danwerner21/CortexPC/images/image1.jpg

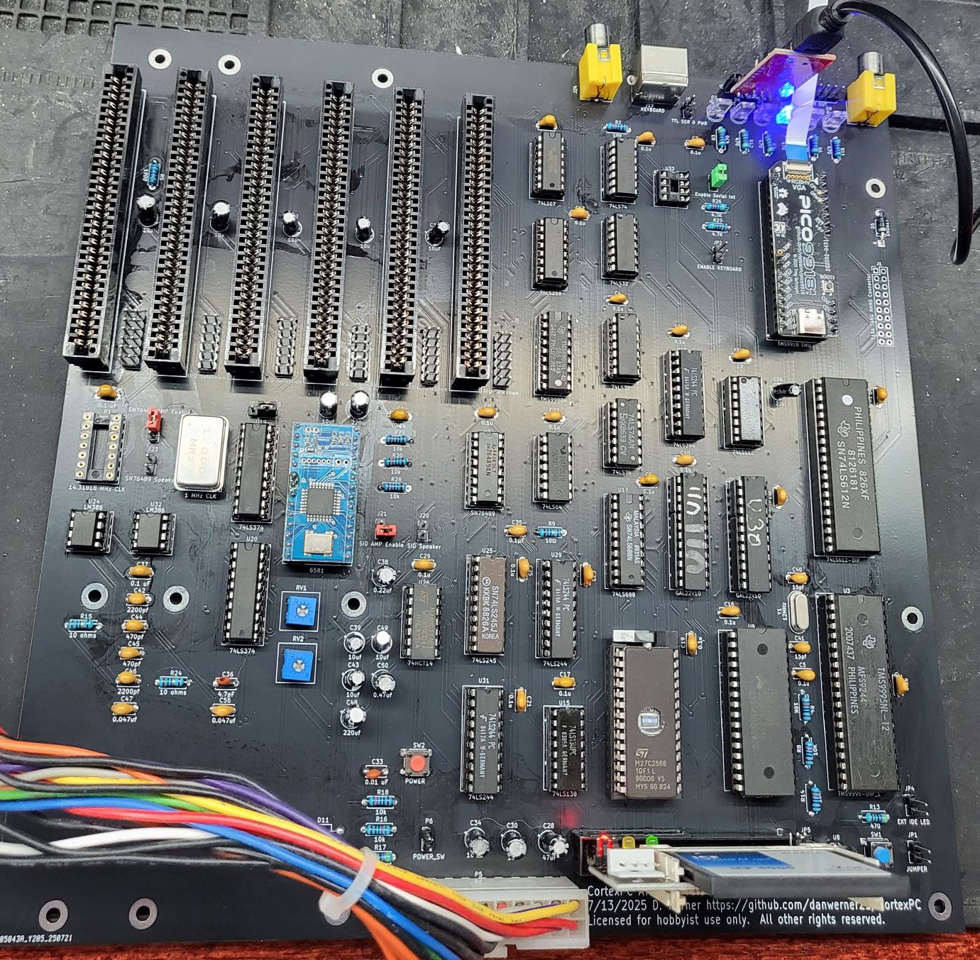
images/image1.jpg
