danwerner21/CortexPC/images/image2.jpg

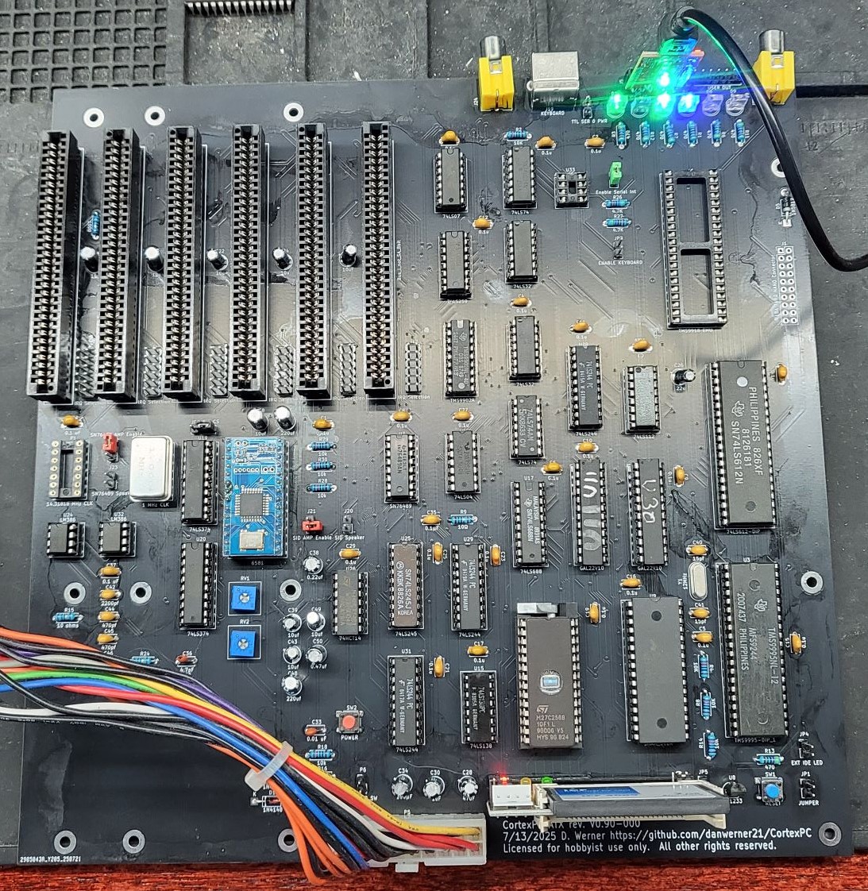
images/image2.jpg
