danwerner21/CortexPC/Hardware/PCB_V0.5.pdf

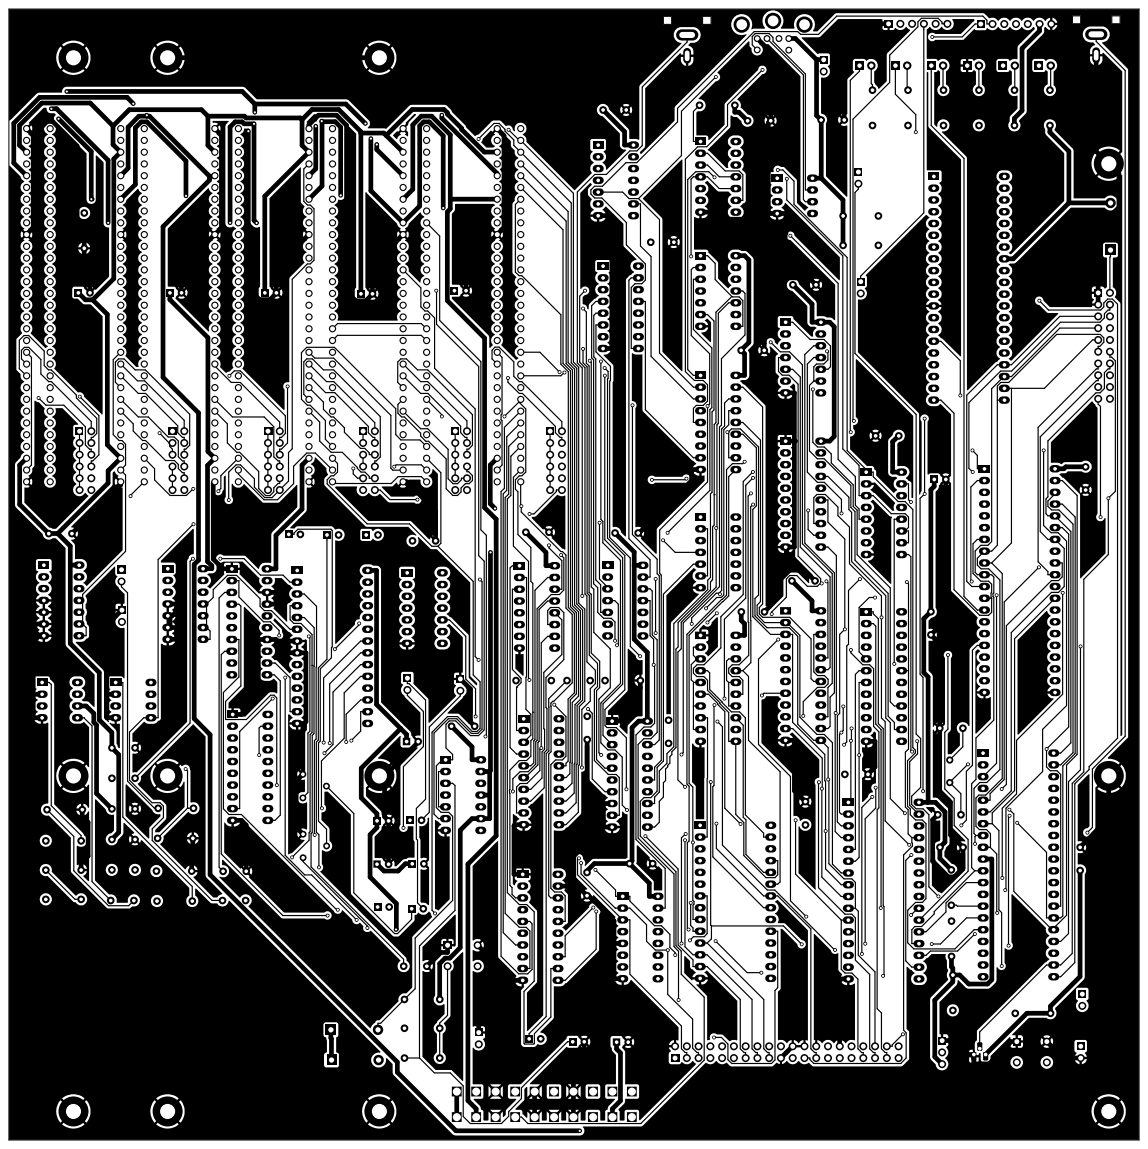
[picture p17: page 1]

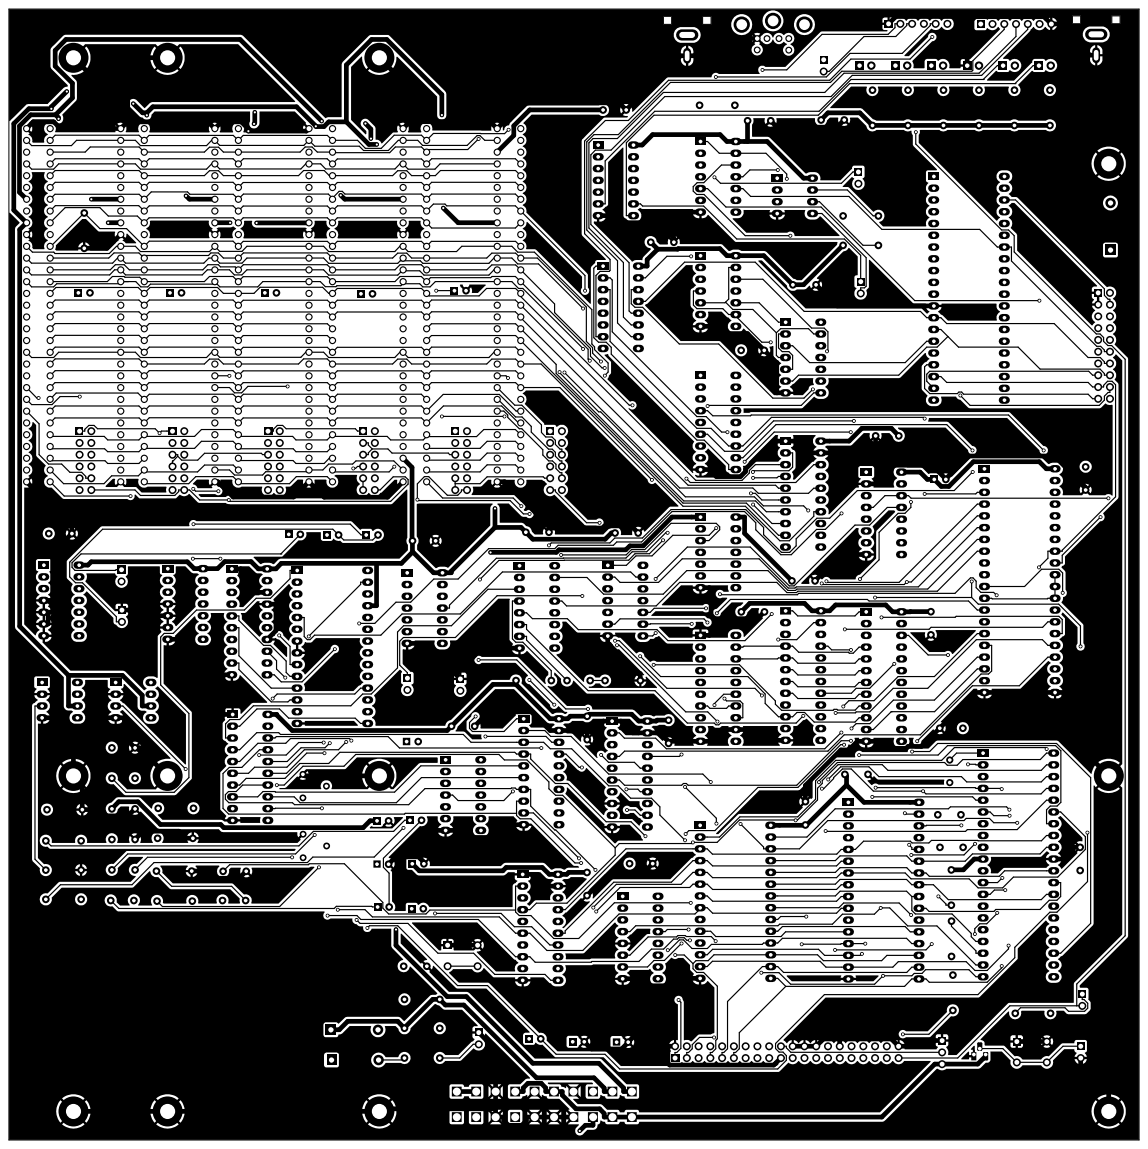
[picture p18: page 2]

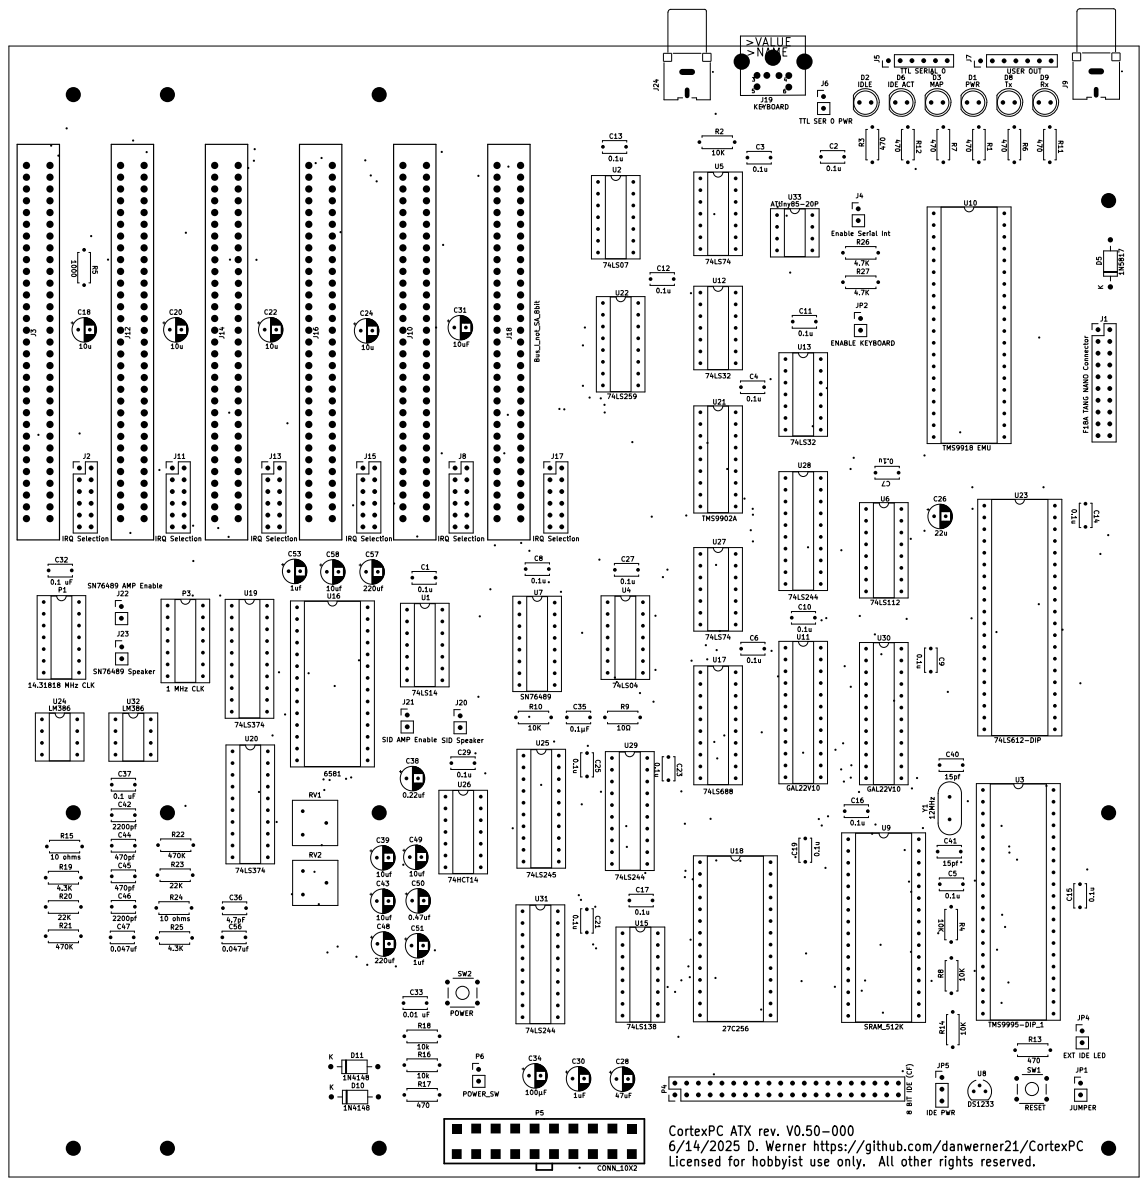
[picture p19: page 3]

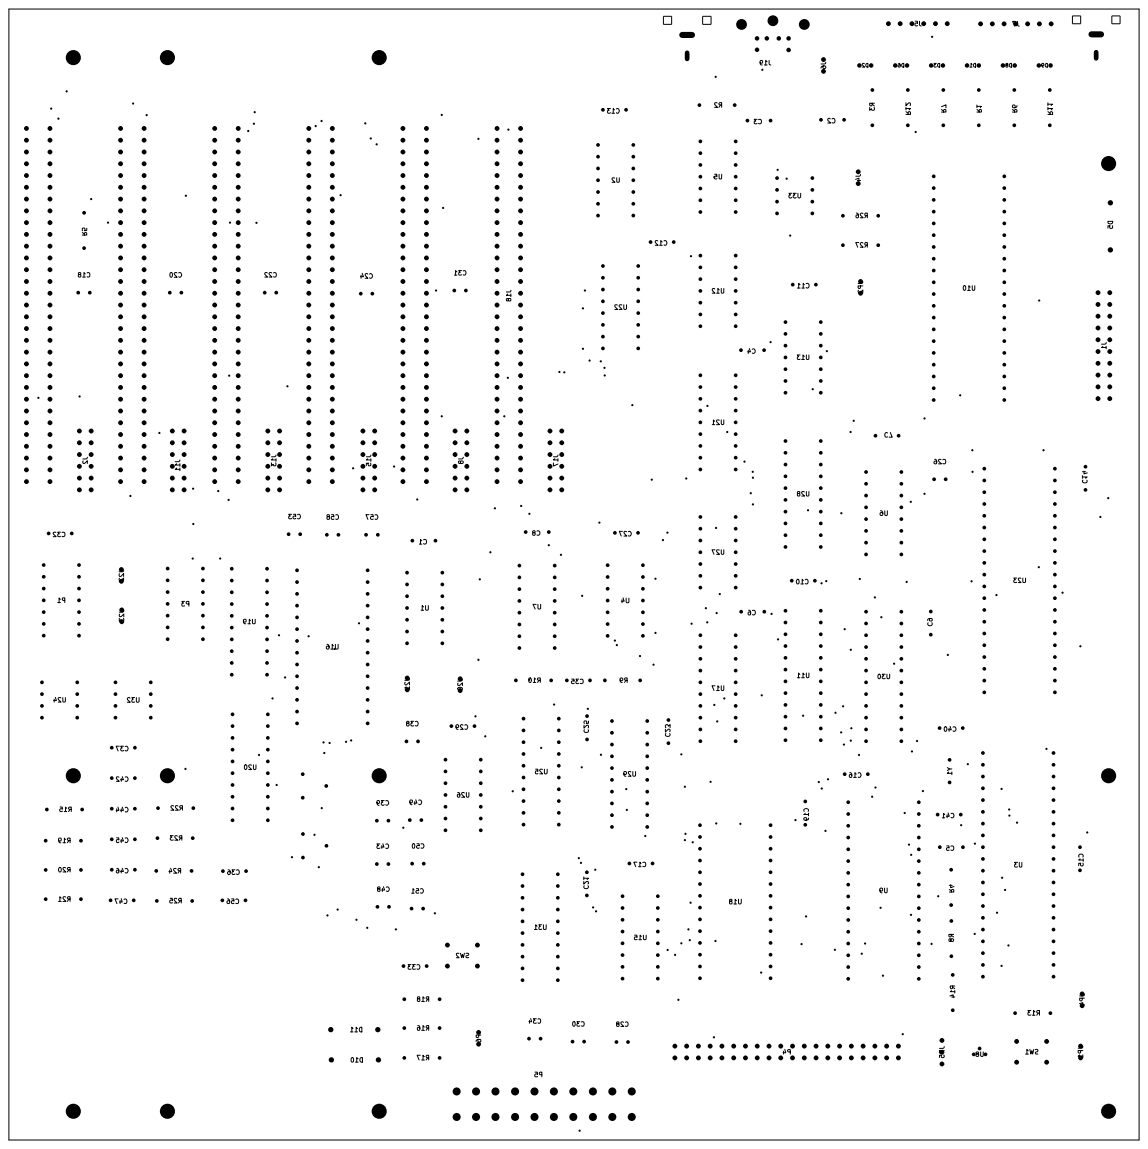
[picture p20: page 4]

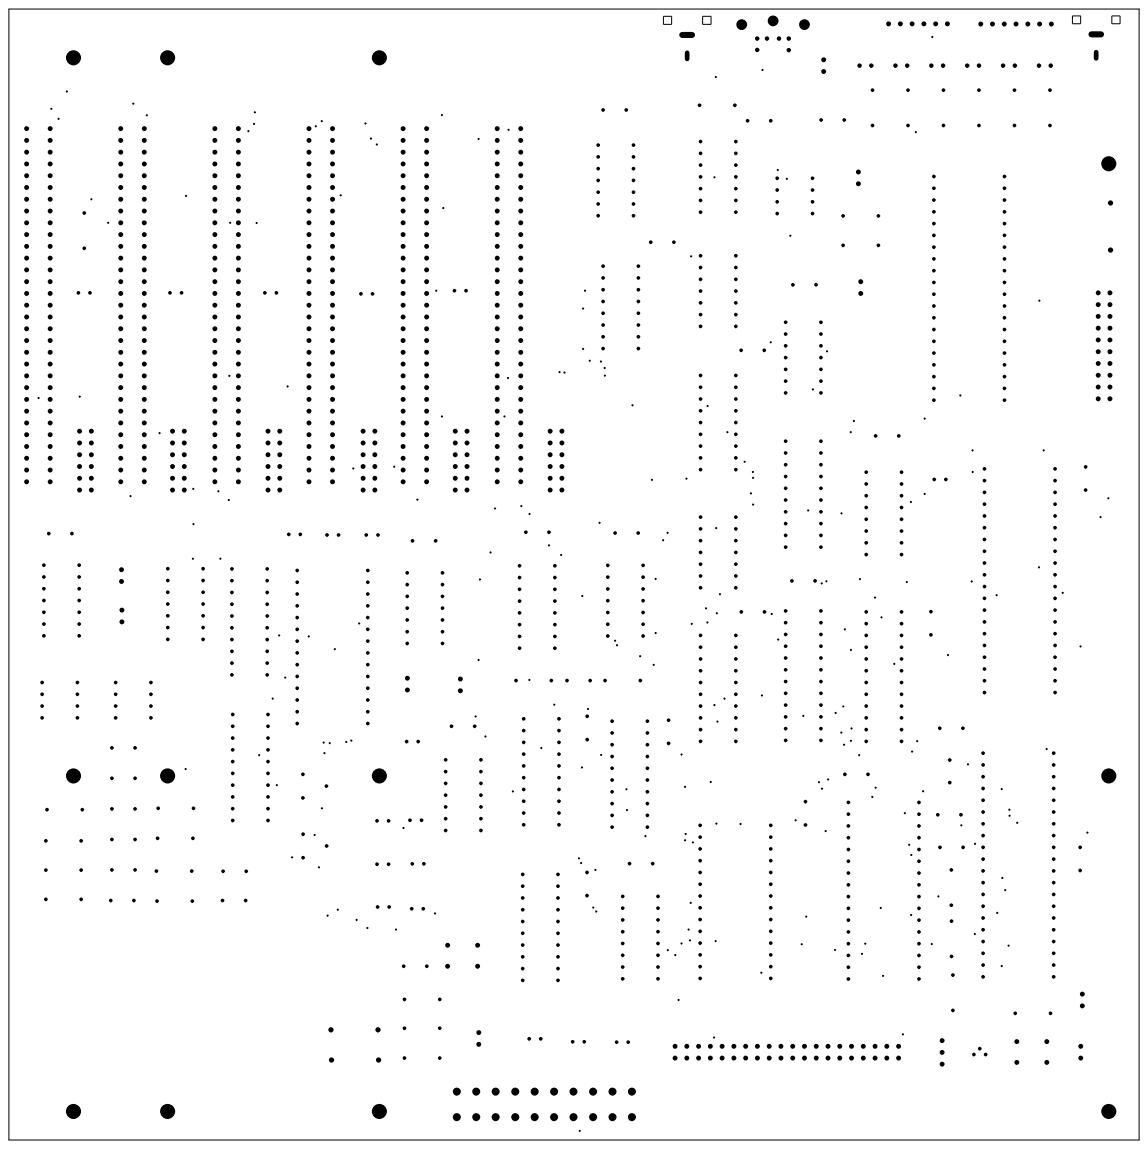
[picture p21: page 5]

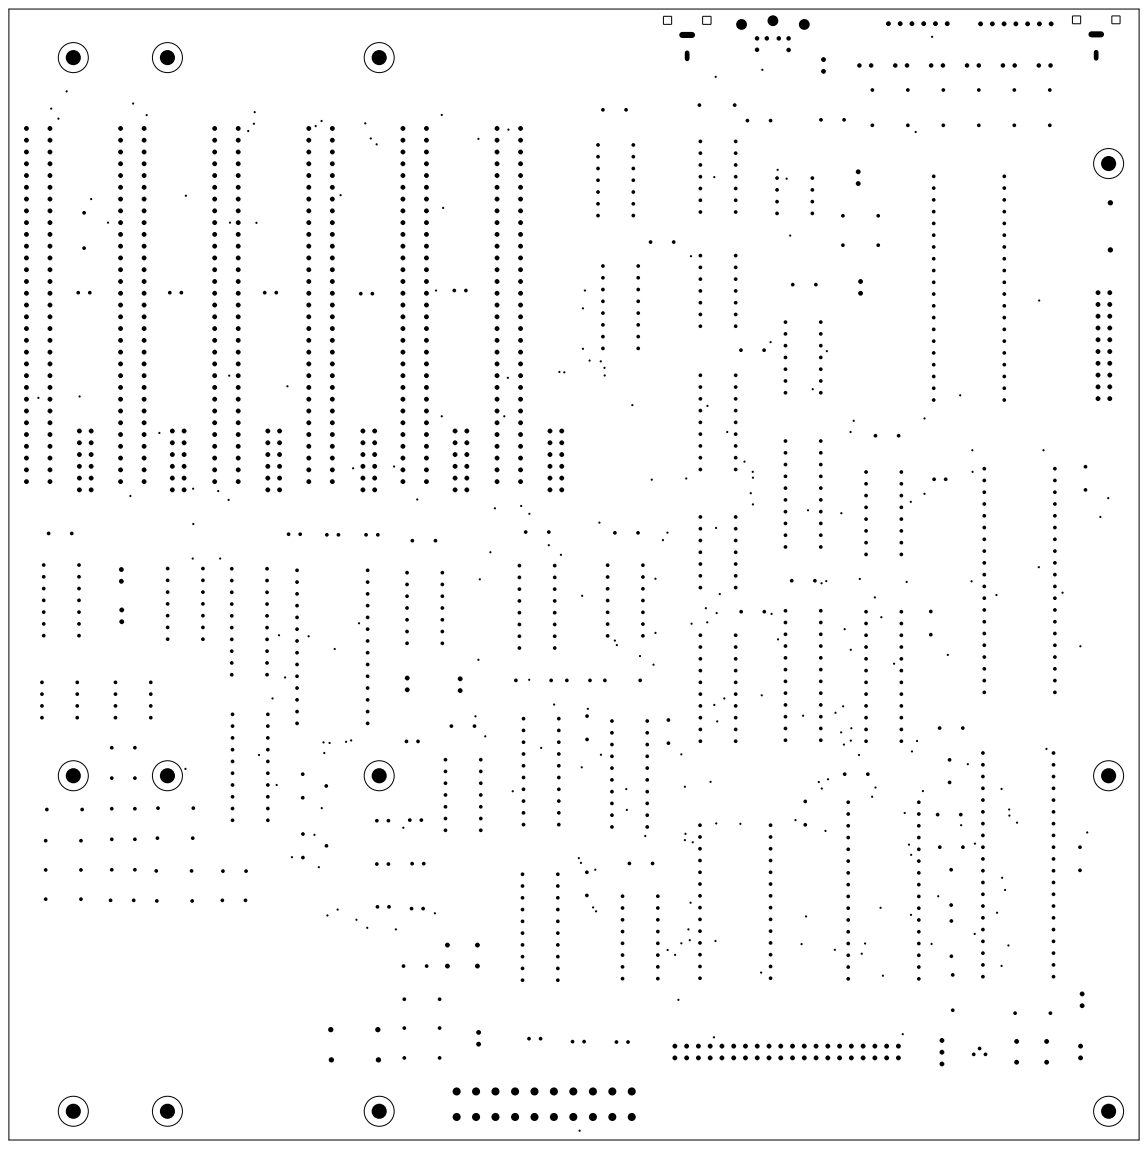
[picture p22: page 6]
