danwerner21/CortexPC/Hardware/Schematic_V0.5.pdf

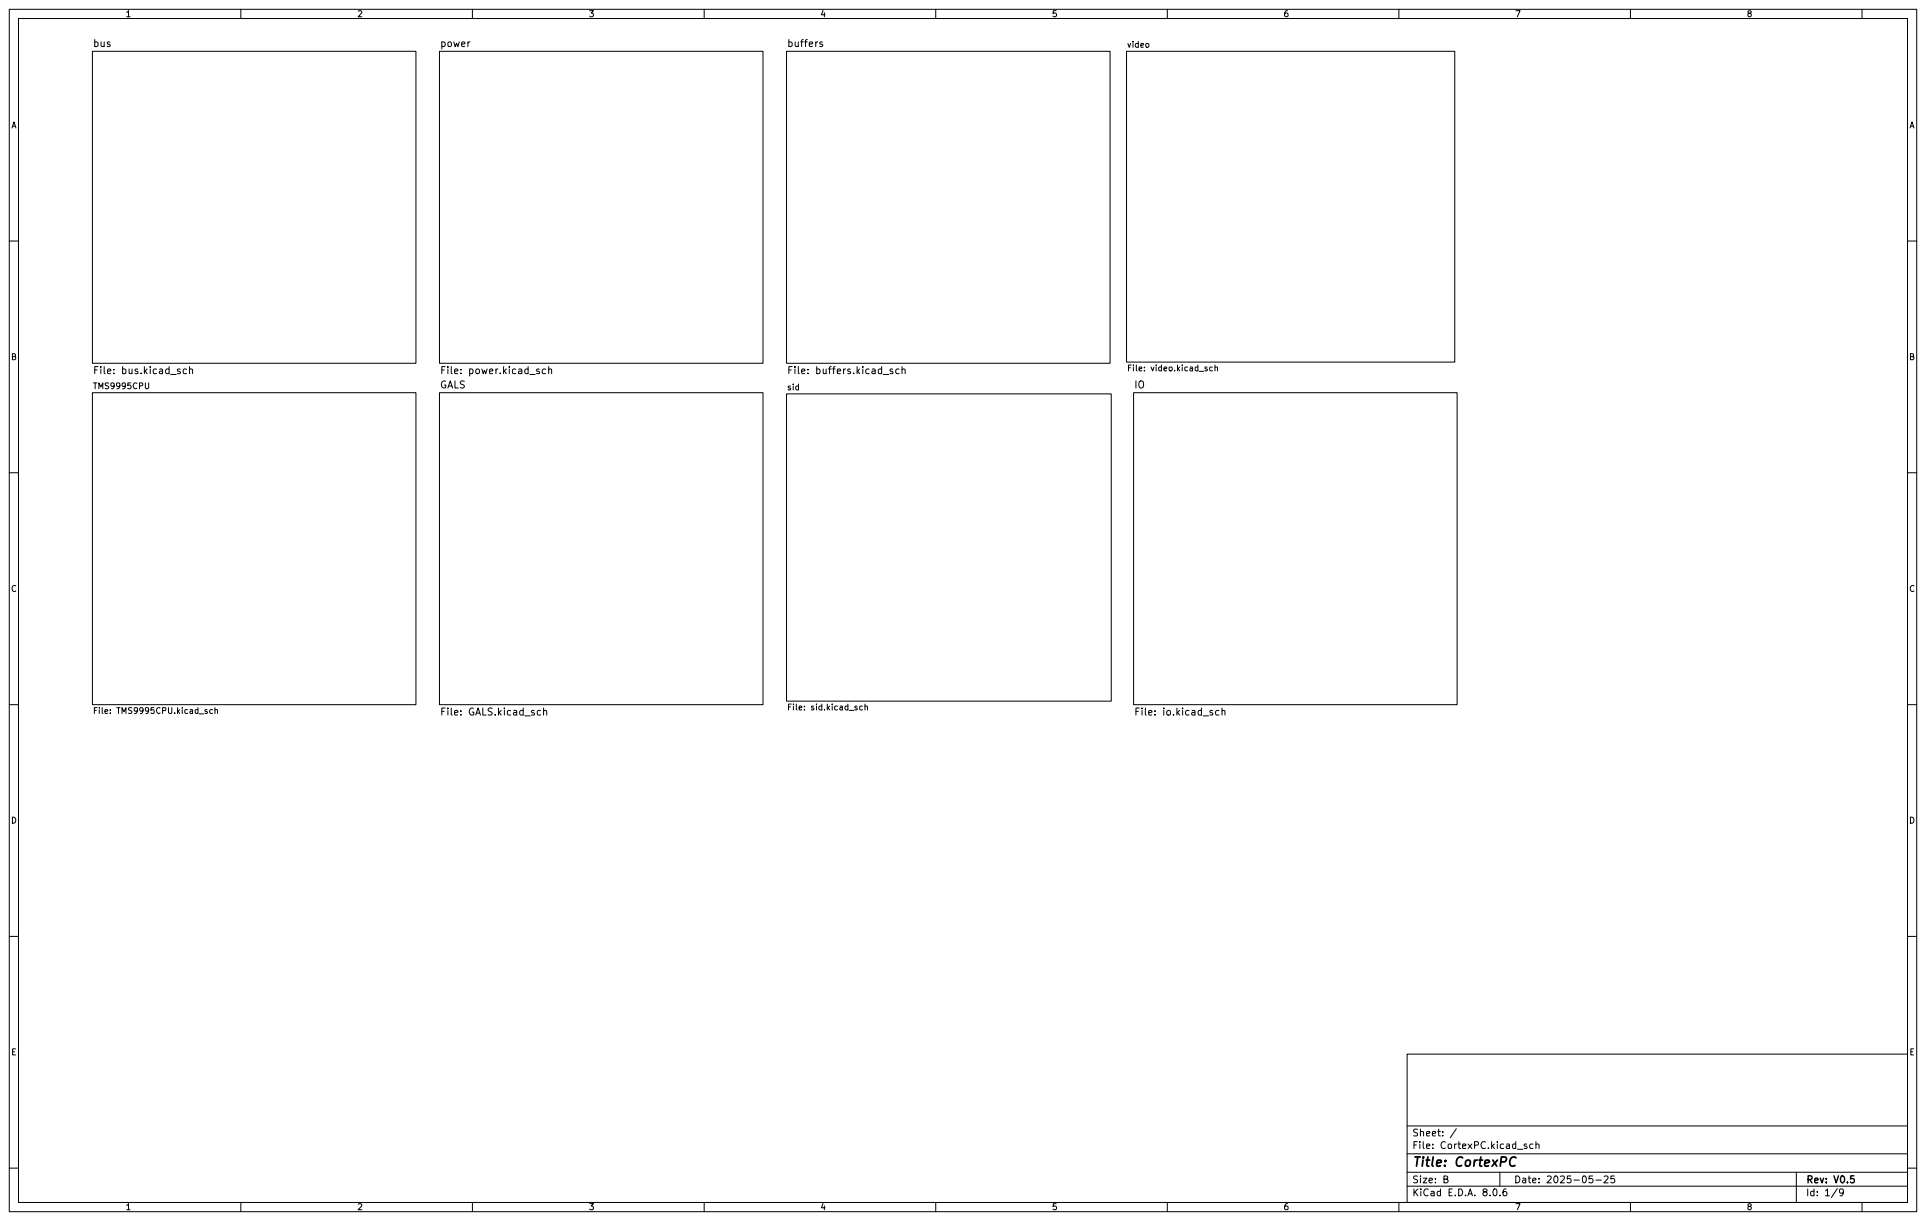
[picture p23: page 1]

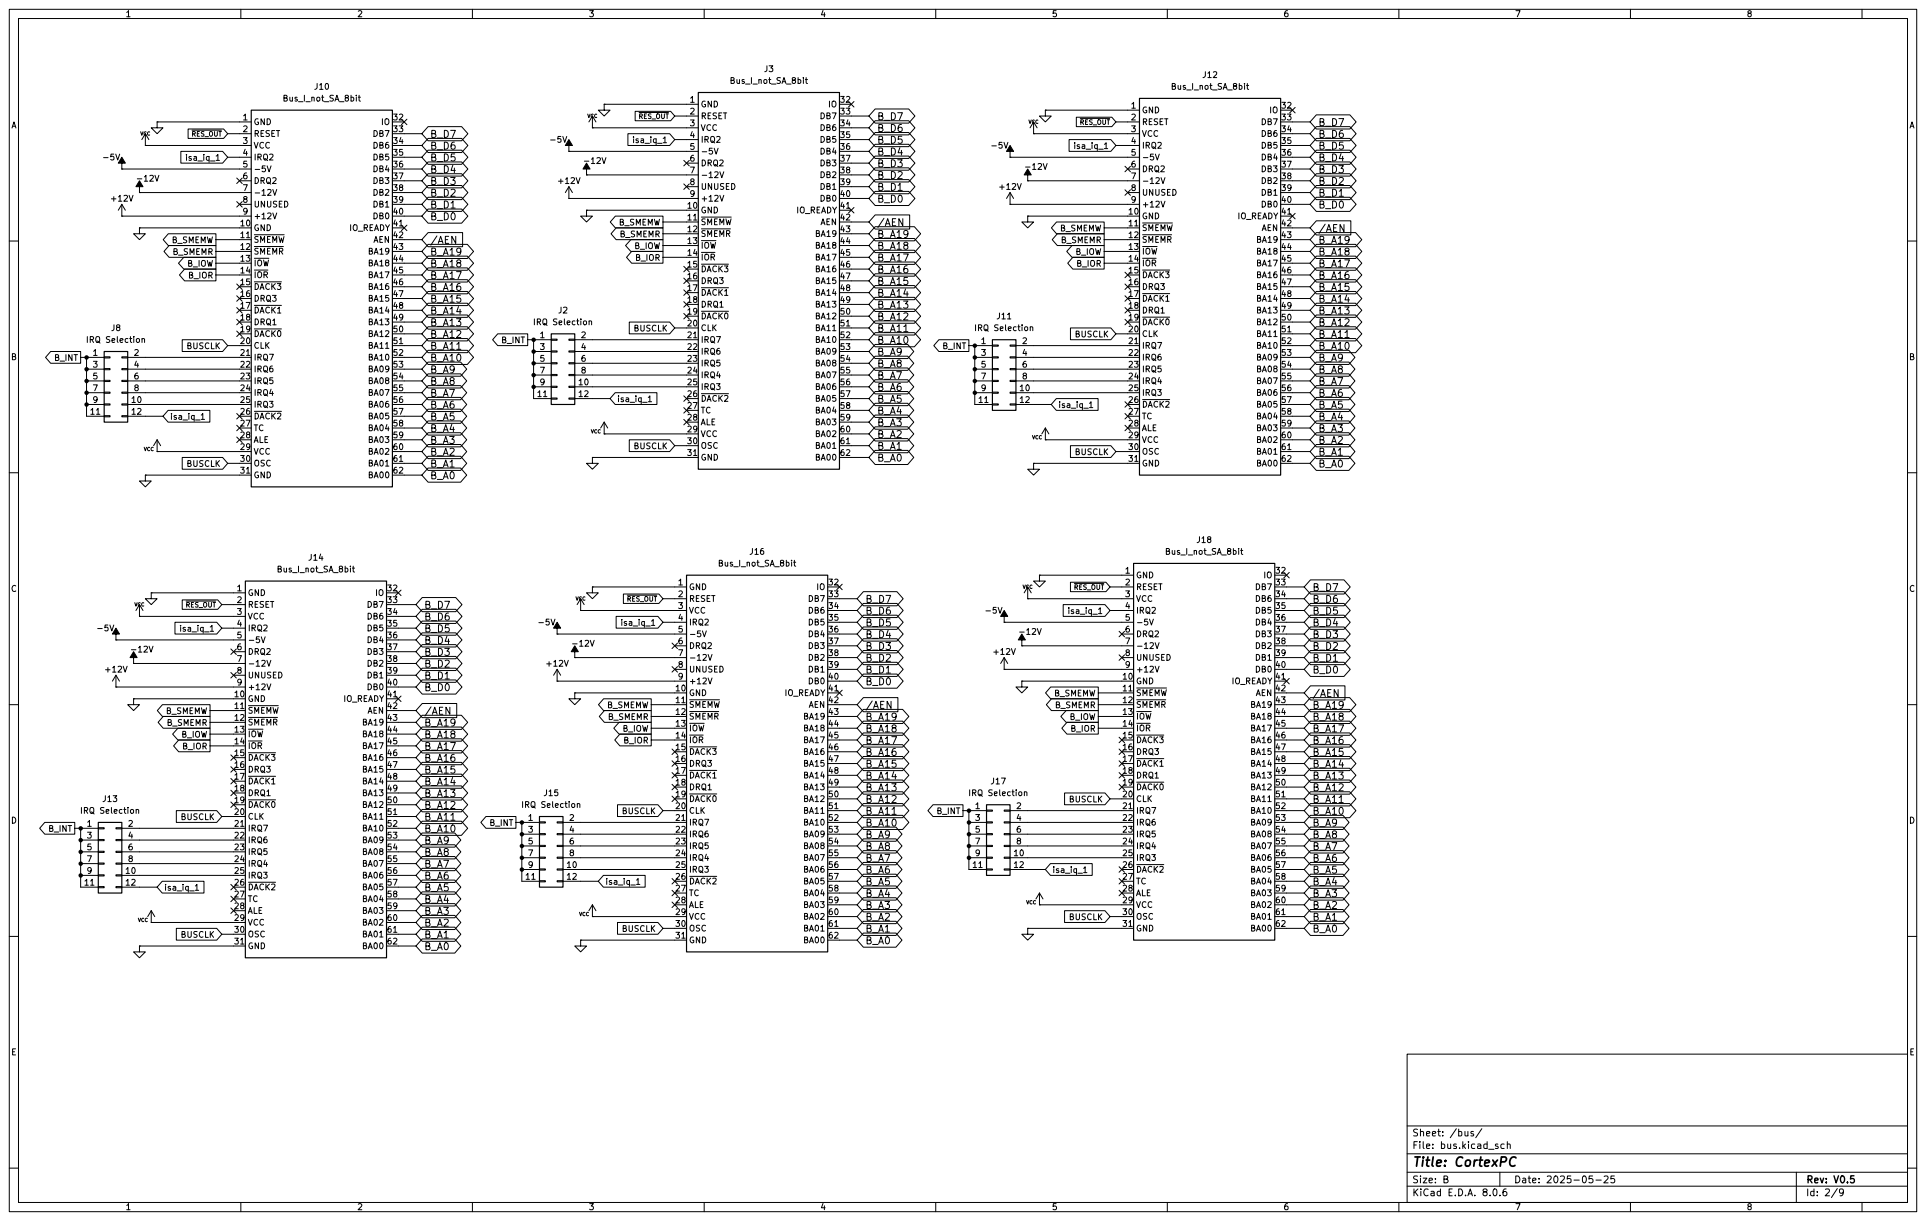
[picture p24: page 2]

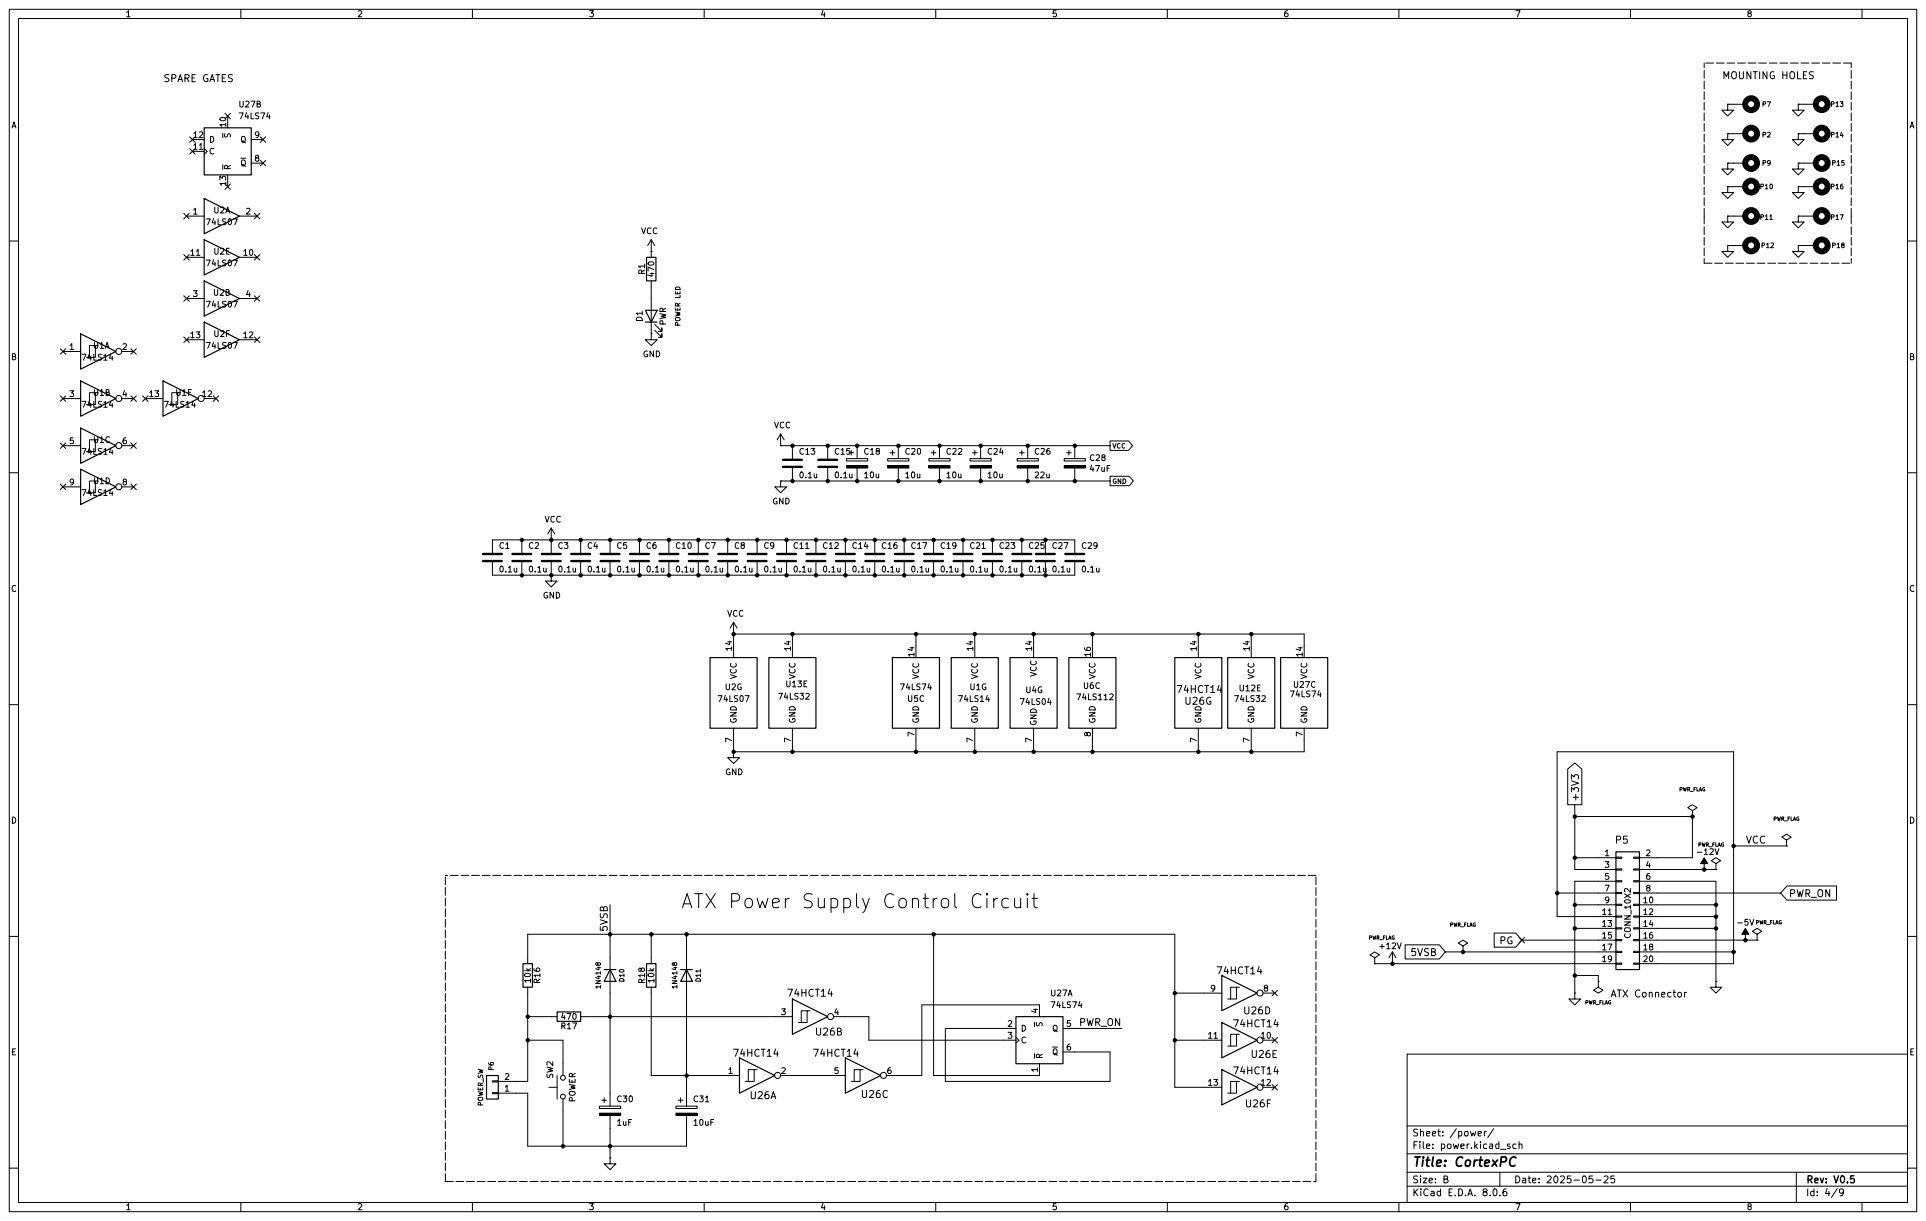
[picture p25: page 3]

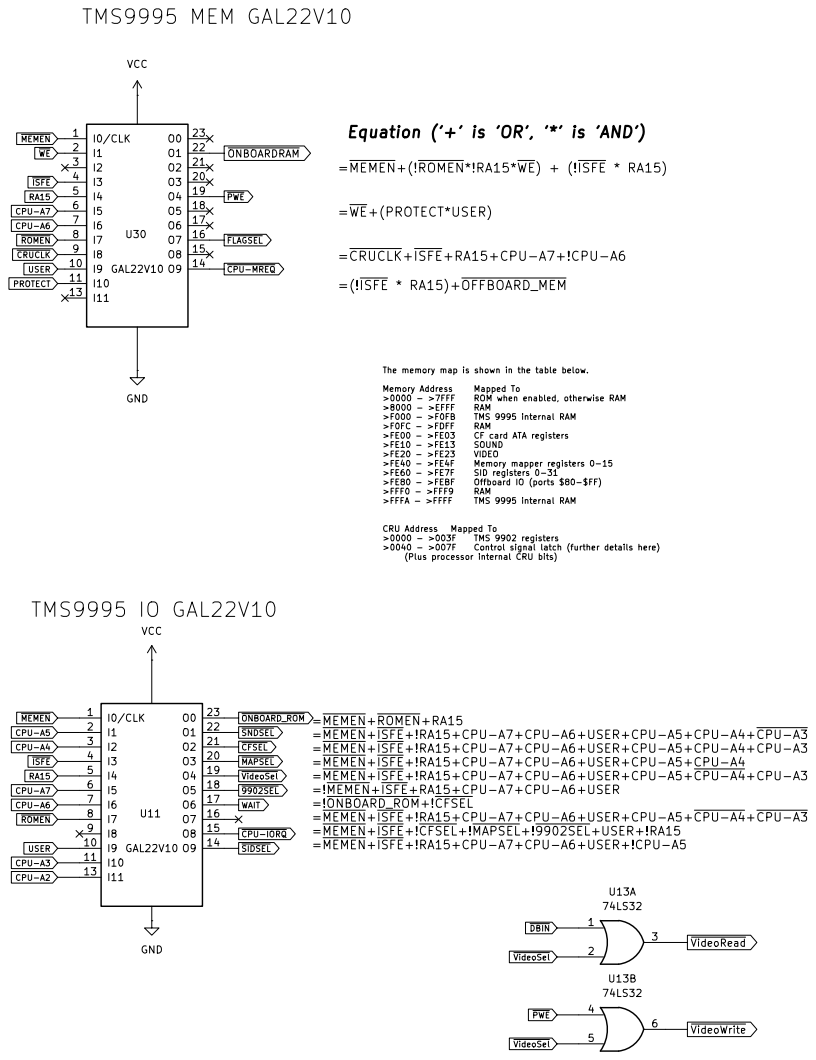
[picture p26: page 4]

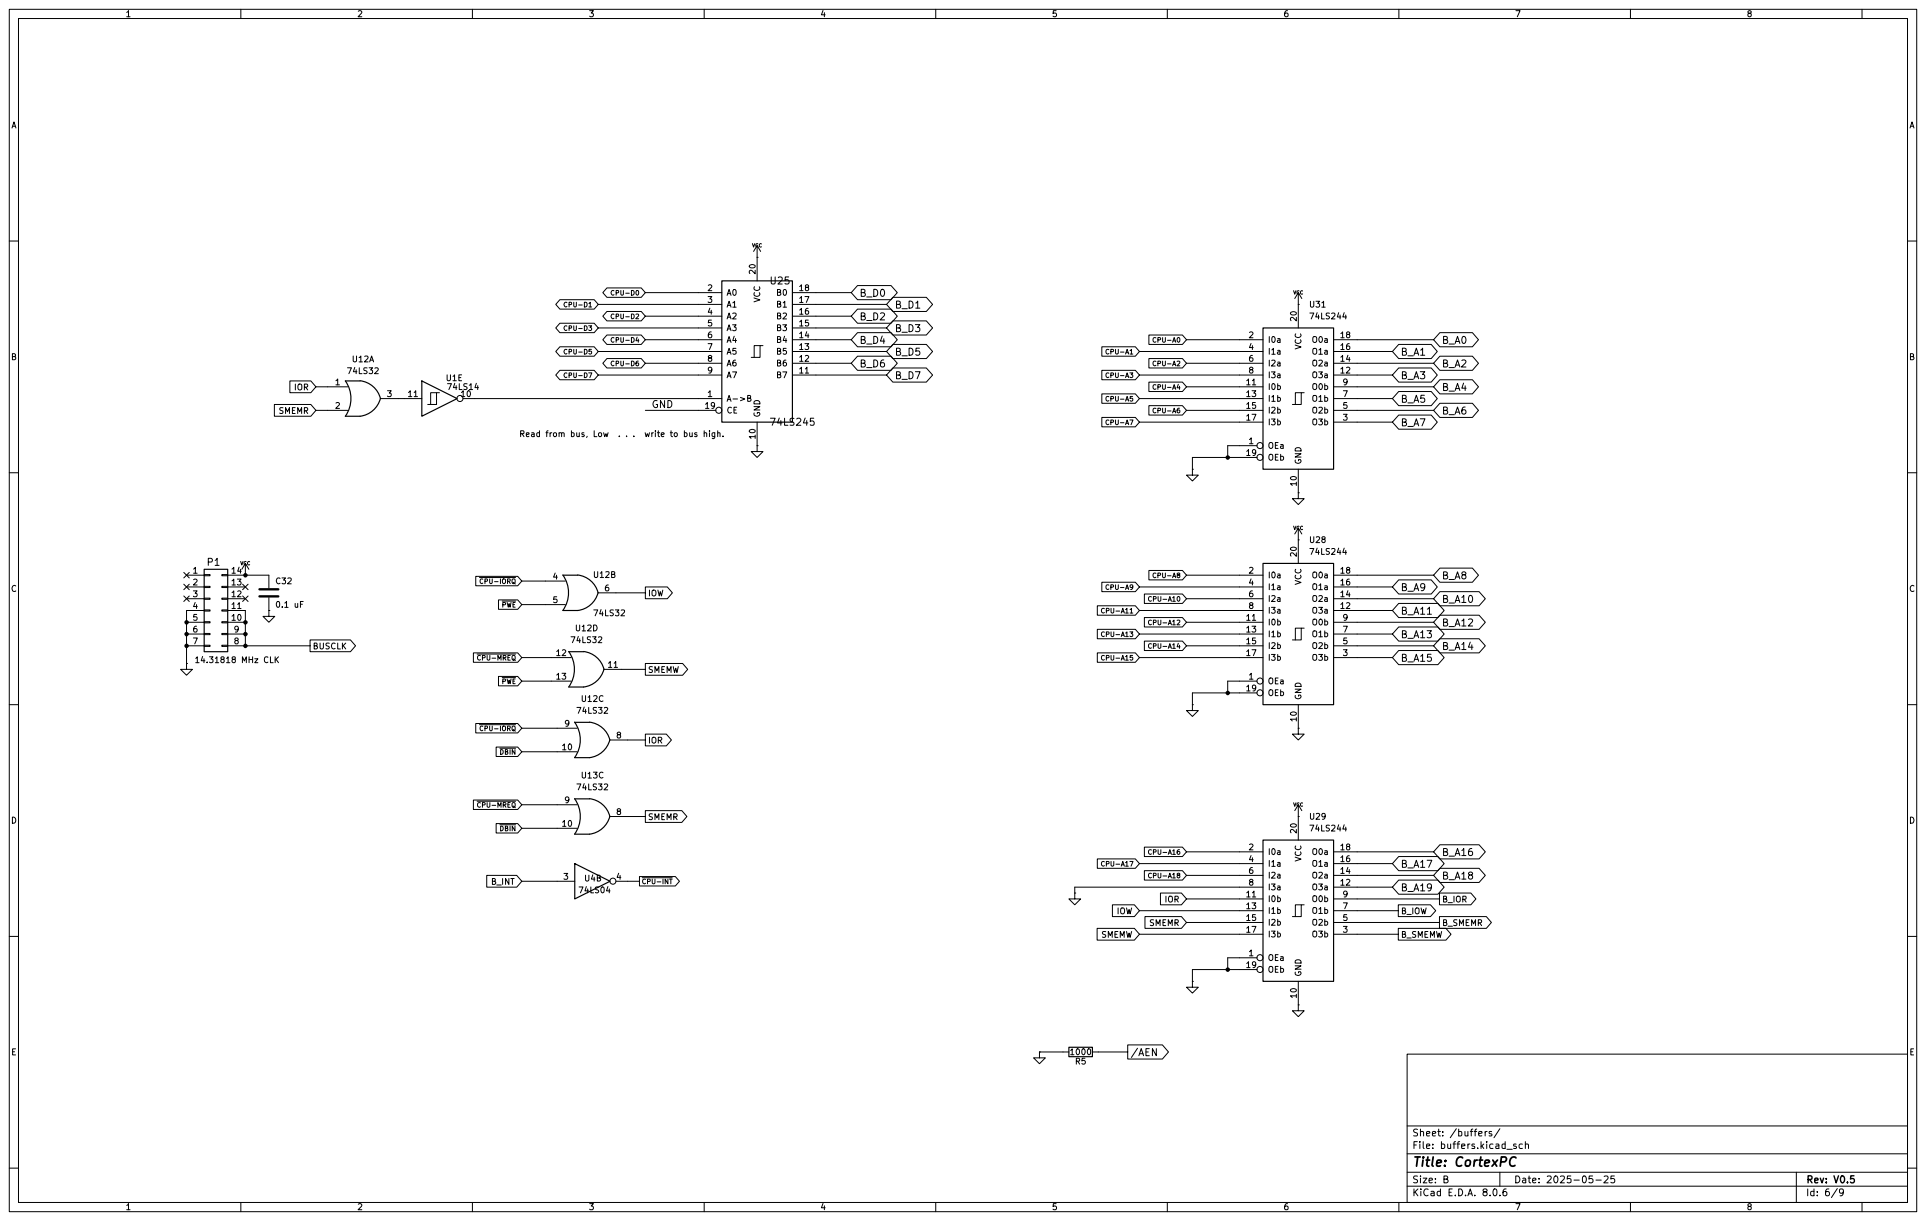
[picture p27: page 5]

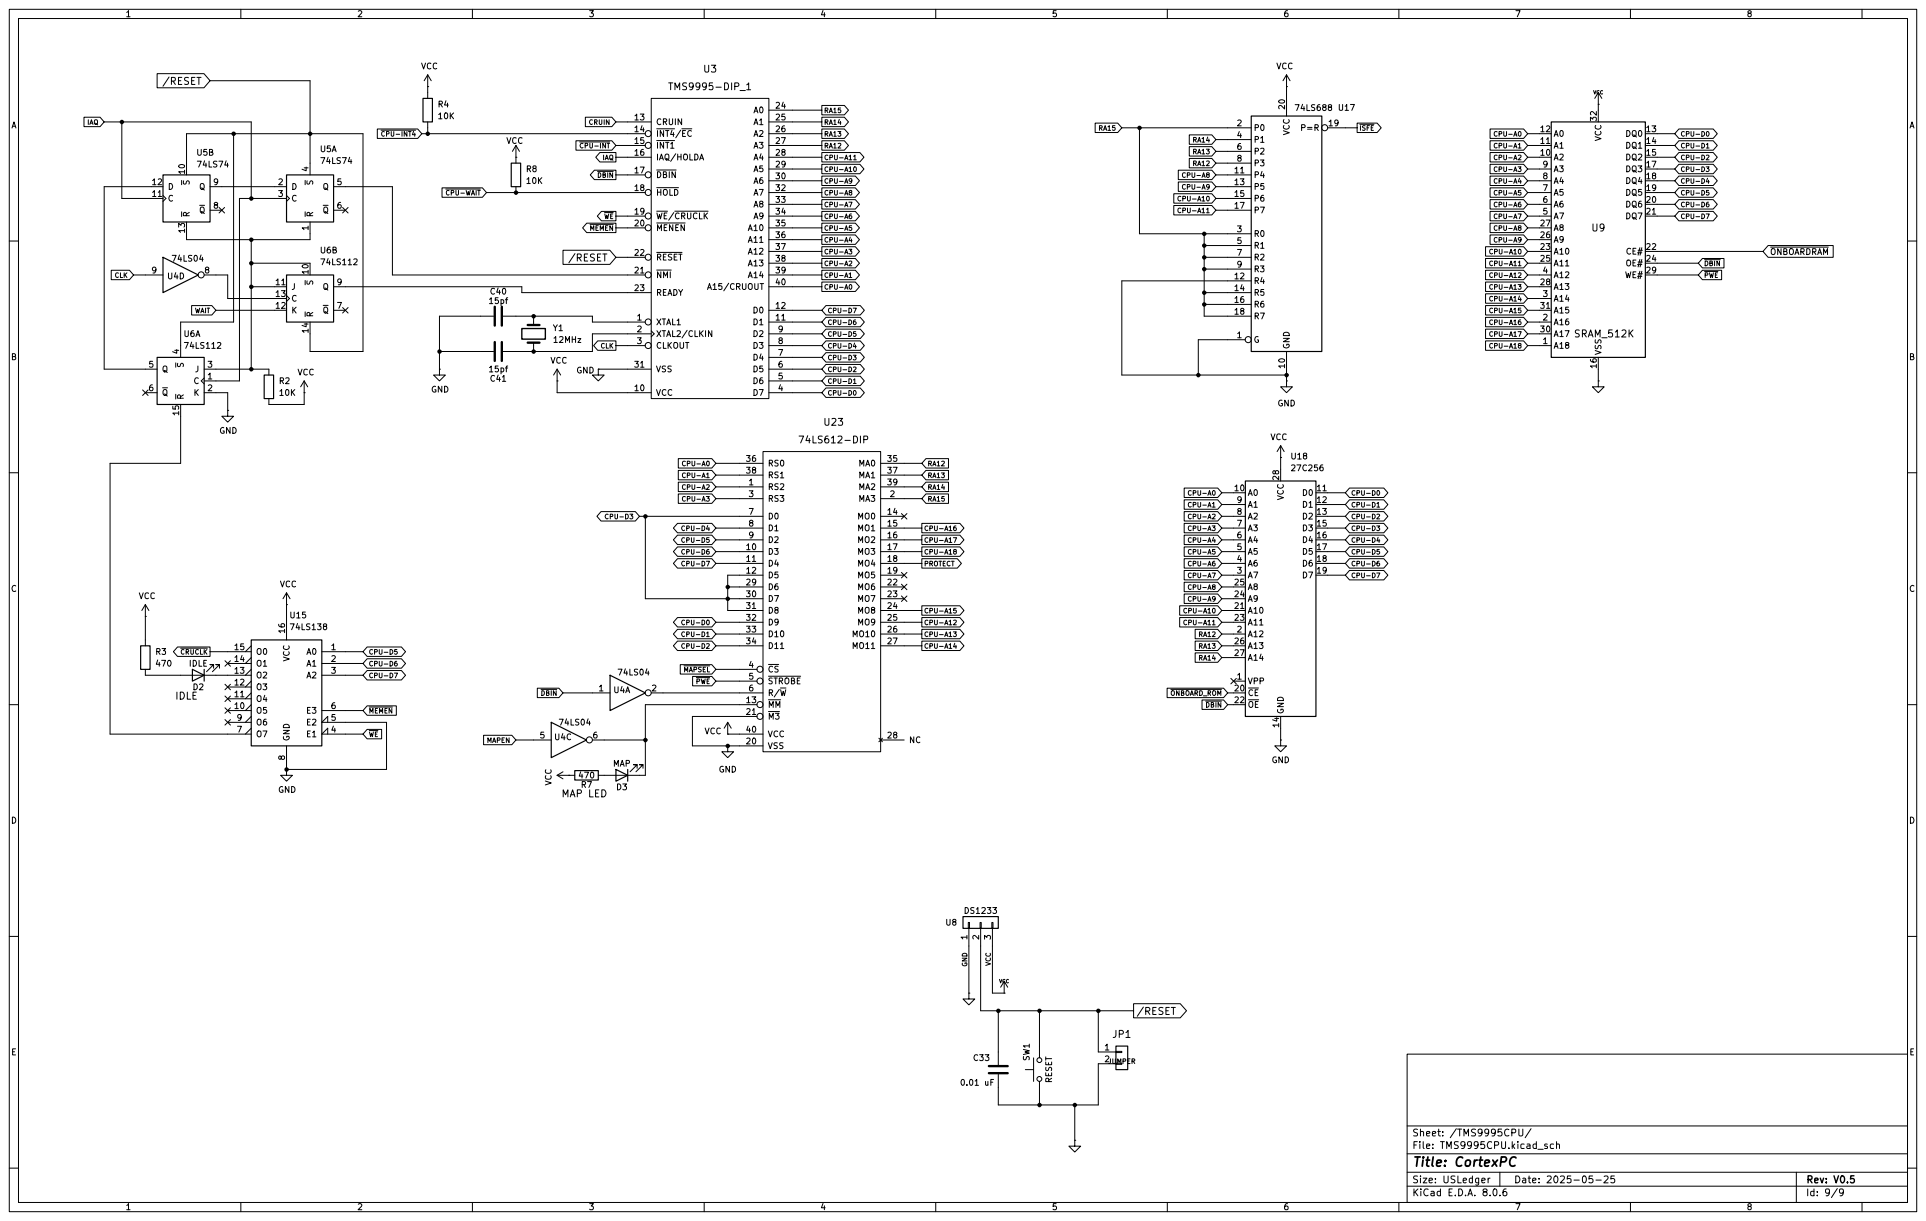
[picture p28: page 6]

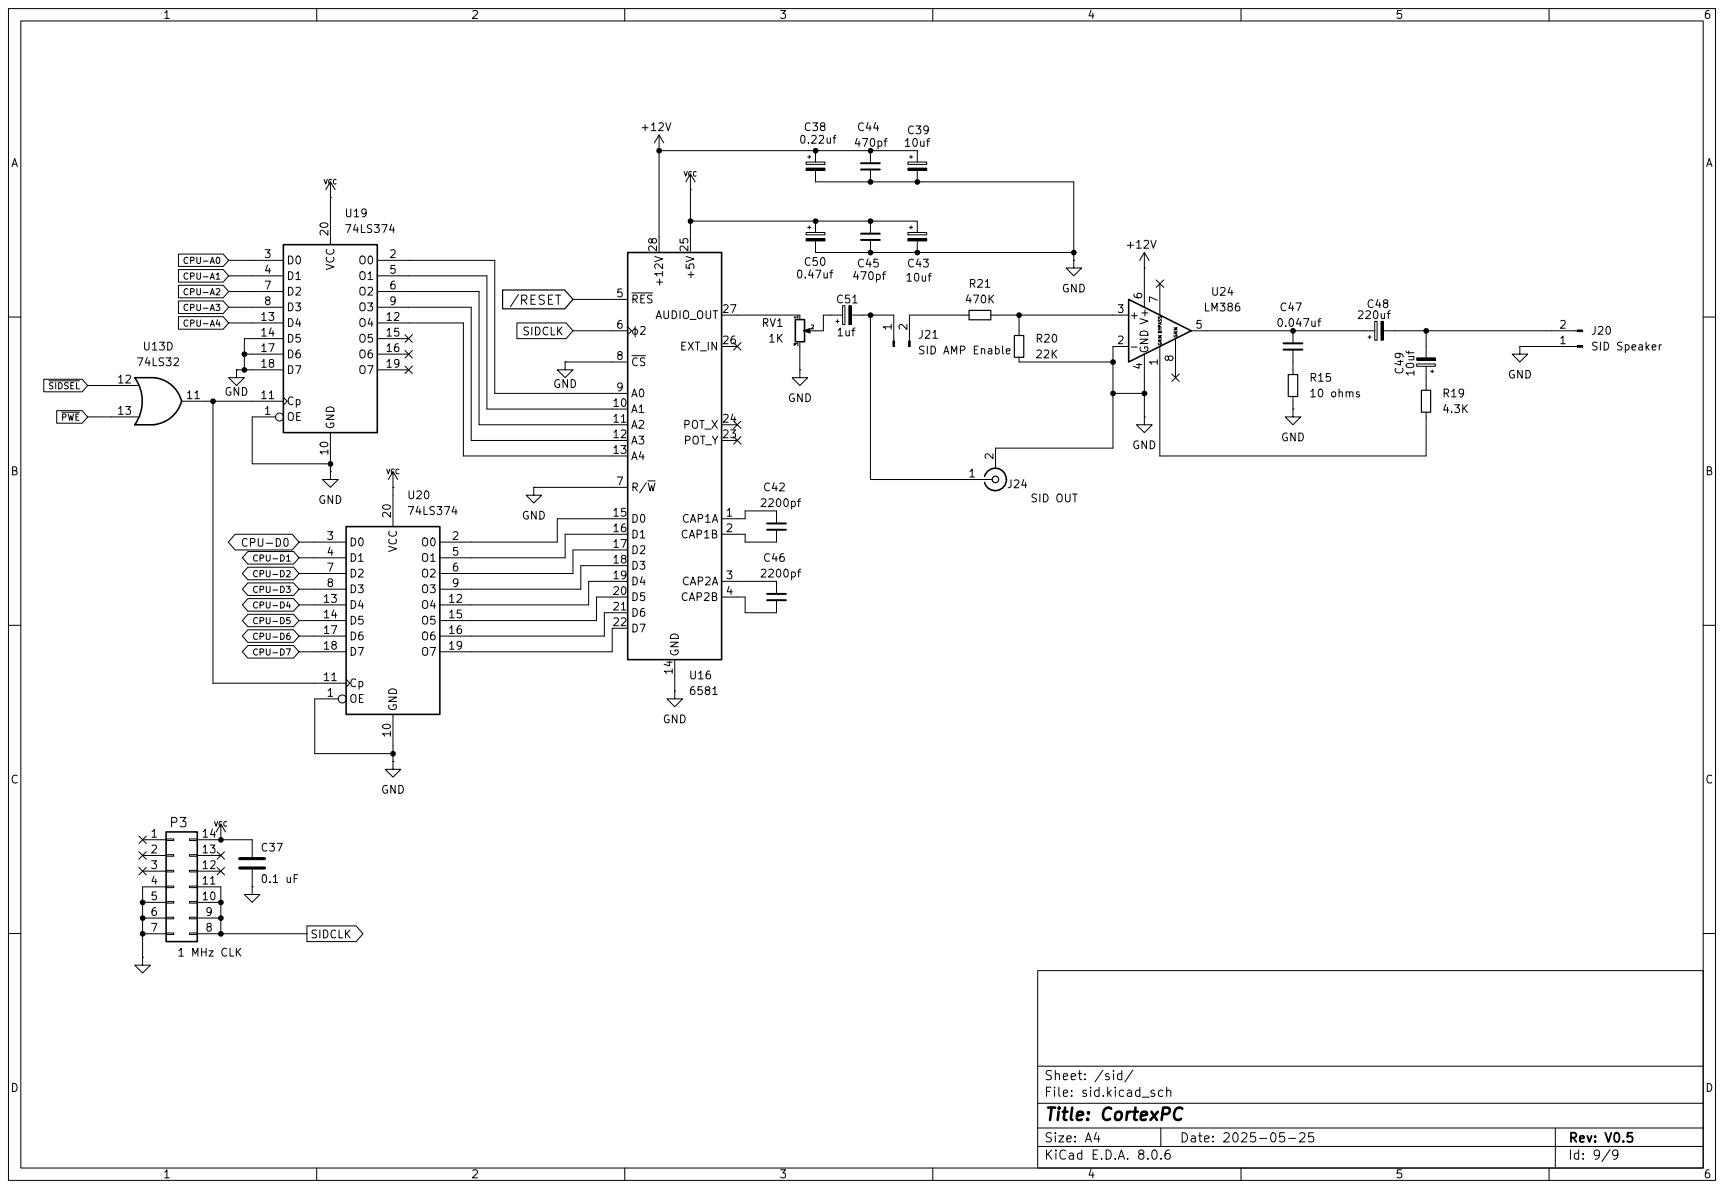
[picture p29: page 7]

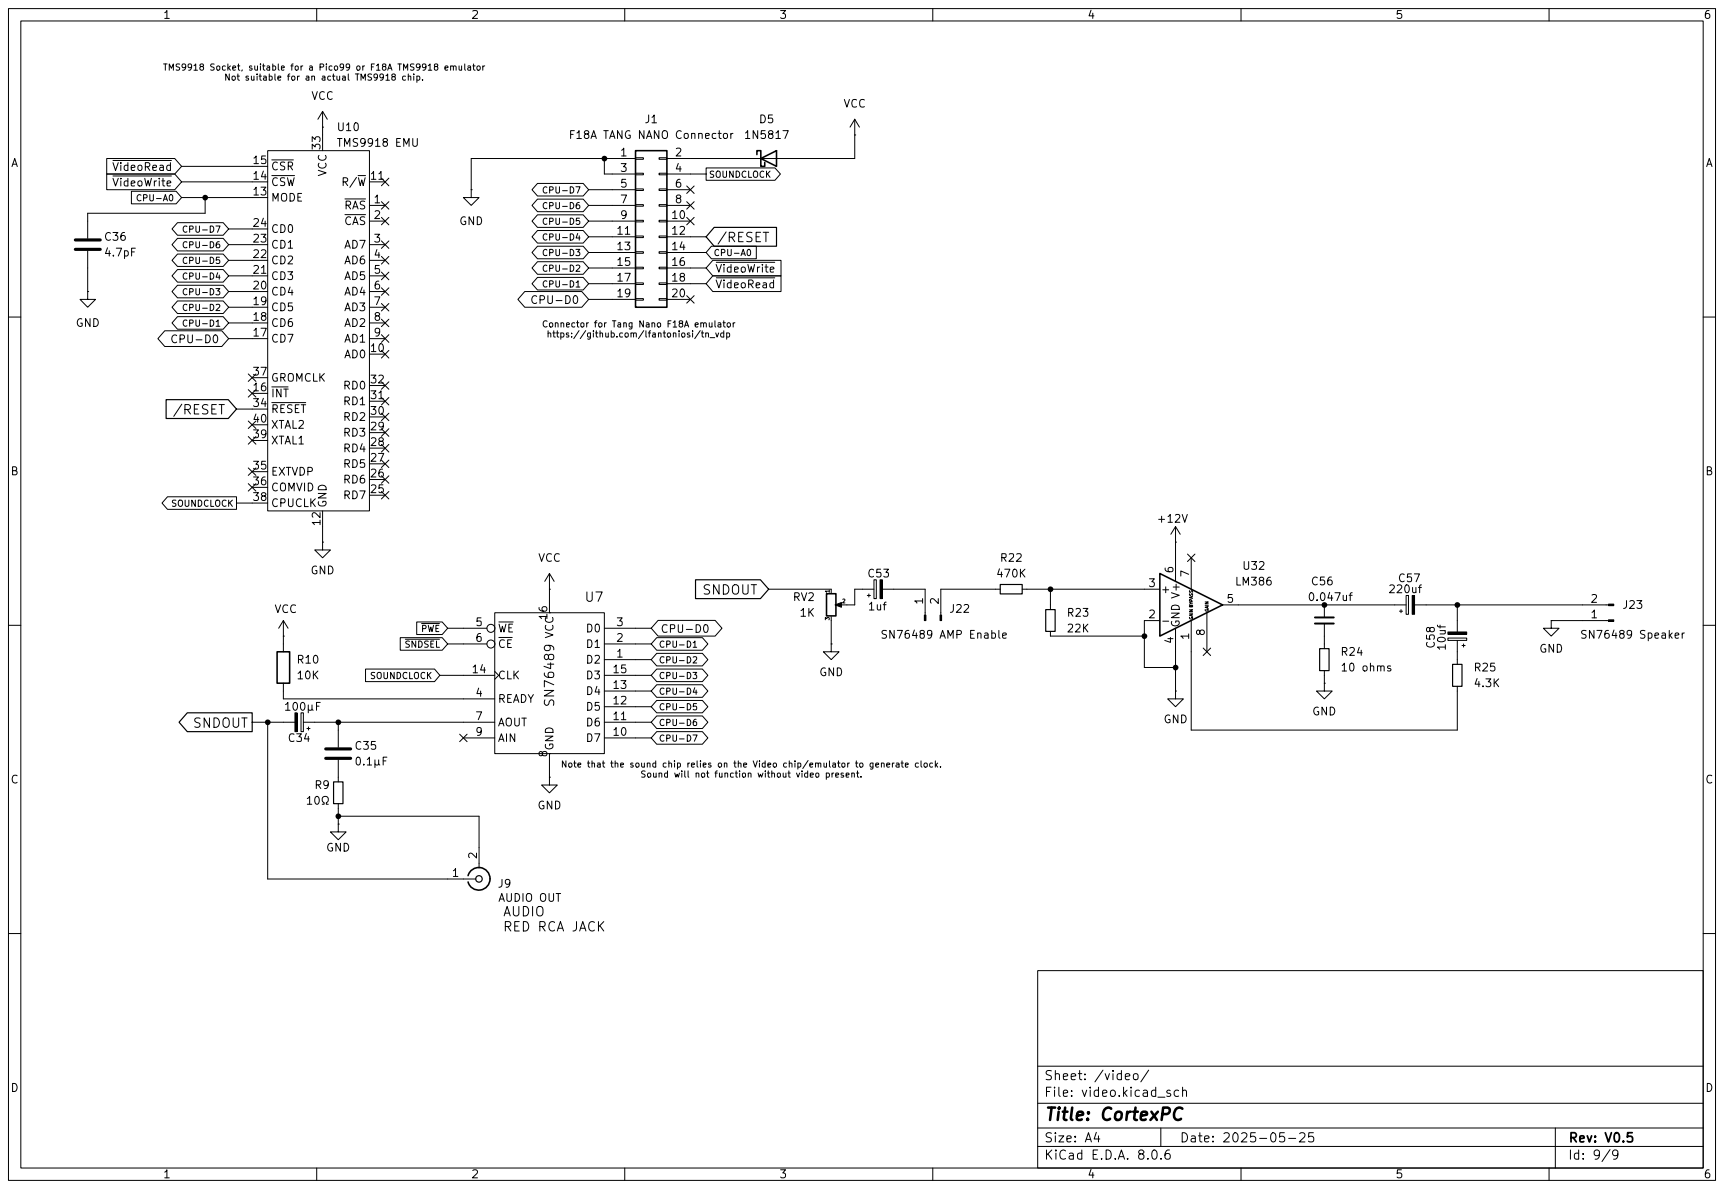
[picture p30: page 8]

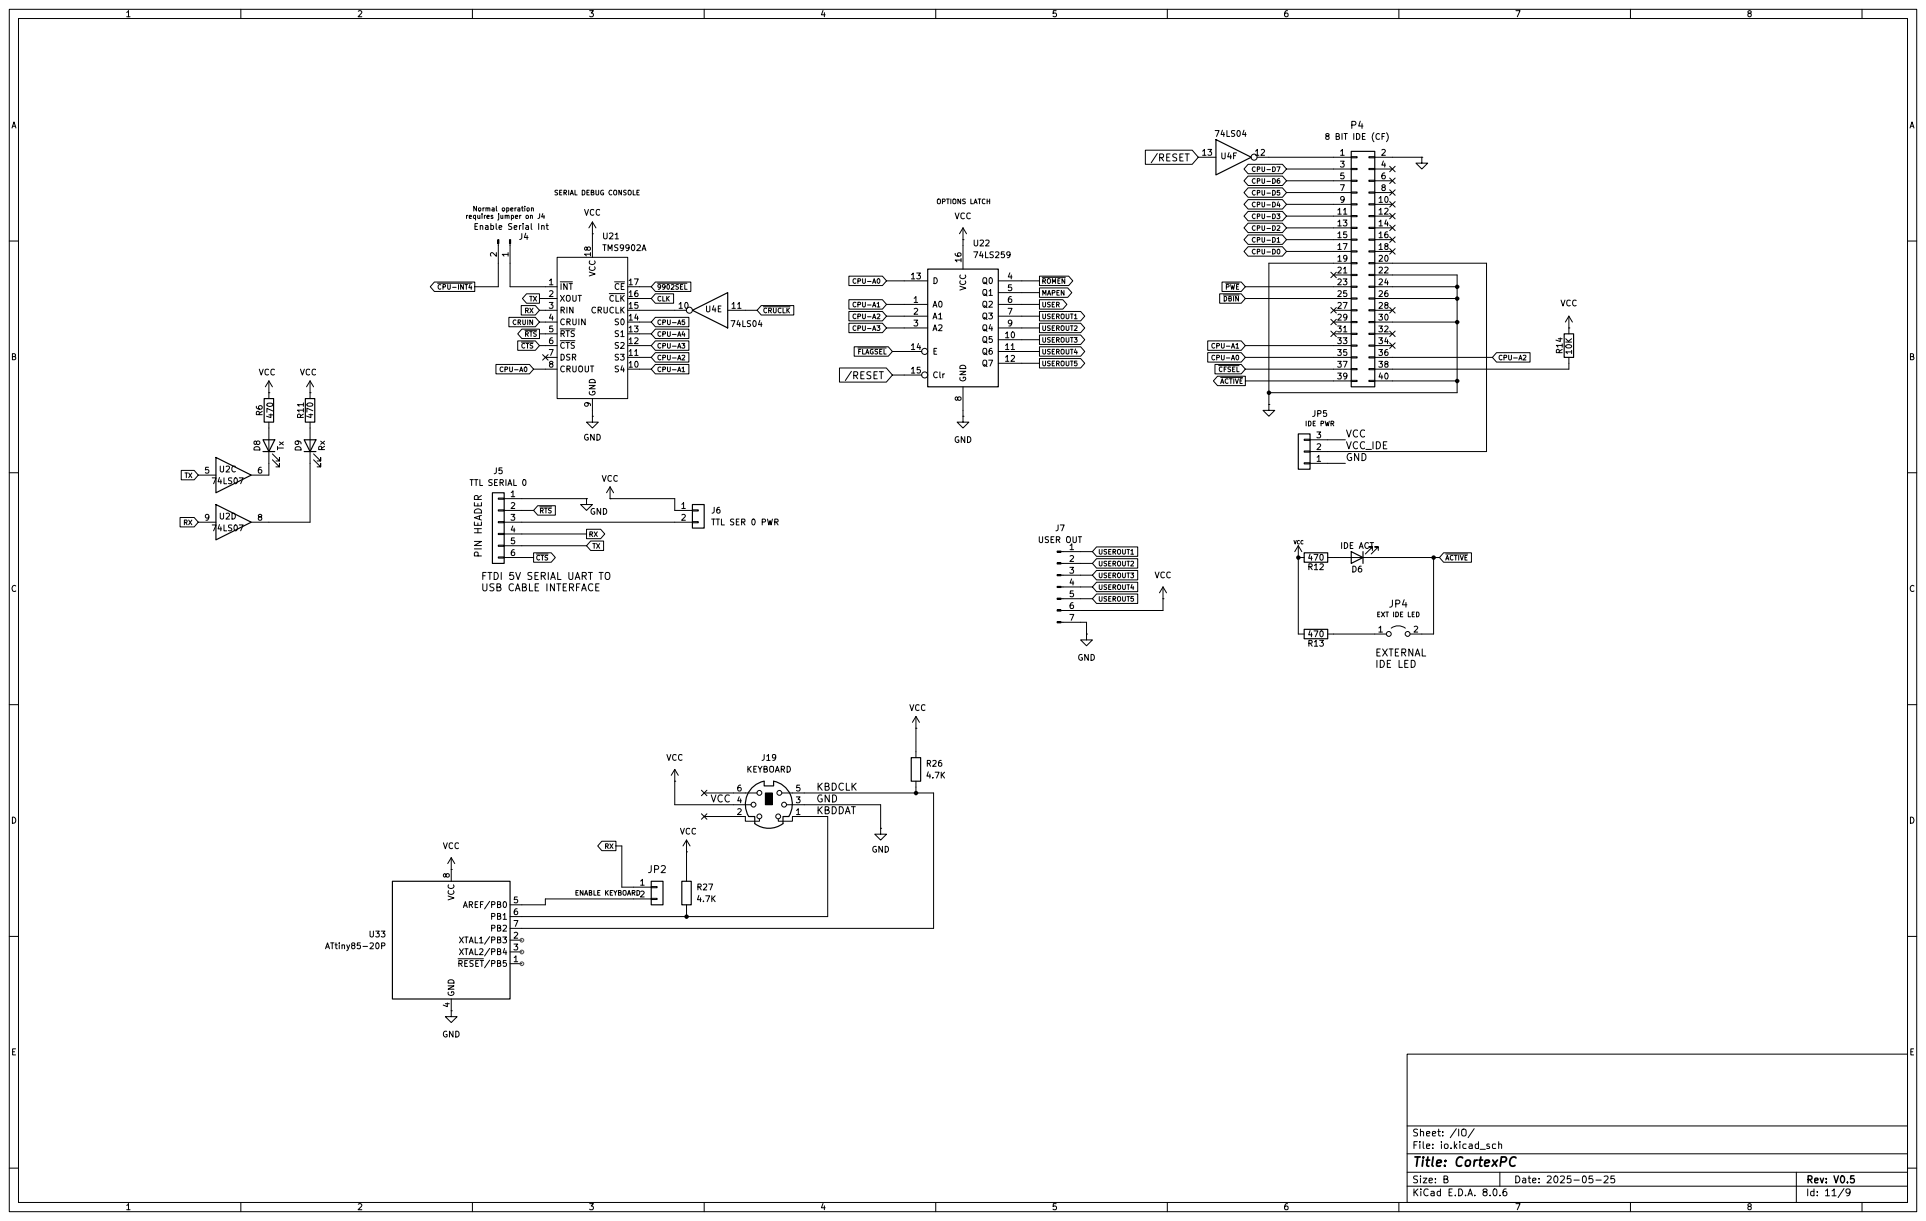
[picture p31: page 9]
