danwerner21/CortexPC/Software/historical informaton/v6unix-1.3.0/as/main.c

#include <unistd.h>
#include <stdlib.h>
#include <stdio.h>
#include <fcntl.h>
#ifndef __ti990__
#include <setjmp.h>
#endif

#include "as.h"

int	nifiles;	/* number of input files    */
char	**ifiles;	/* names of input files     */
int	cfile = -1;	/* index of current file    */
int	fd_in;		/* fd of current input file */

int	pass	 = 0;	/* pass number */
int	pass_gen = 0;	/* generate code in this pass ?    */
int	pass_lst = 0;	/* generate listing in this pass ? */
int	textlen  = 0;	/* length of text segment in current run */
int	lflag	 = 0;	/* listing */

char *ofname = "a.out";

char *usage = "Usage: as [-o object-file] [-u] [-l] input-file [...]\n";

#ifndef __ti990__
jmp_buf err_jmp;
#endif
  
int main(argc, argv)
	int argc; char **argv;
{
	sym_init();
	/* Get flags & files */
	while (--argc > 0 && **++argv == '-') {
		switch (argv[0][1]) {
		case 'u':
			uflag++;
			break;
		case 'l':
			lflag++;
			break;
		case 'o':
			if (--argc == 0 || **++argv == '-') {
				printf("No object filename\n");
				exit(1);
			}
			ofname = *argv;
			break;
		}
	}
	if ((nifiles = argc) < 1) {
		printf("%s", usage);
		exit(1);
	}
	ifiles = argv;

	/* symbol table generation pass */
	assemble();
	if (errcnt)
		exit(errcnt);

	/*
	 * Code generation pass(es)
	 *	- more than one pass may be required in cases
	 *	  where short jump instructions must be changed
	 *    a reverse jump over a long distance branch.
	 *	  Since each pass can only make instructions longer, the
	 *	  process is guaranteed to terminate eventually.
	 */
	do {
		pass++;
		textlen = text.loc;
		cfile   = -1;
		assemble();
		if (errcnt)
			exit(errcnt);
	} while ( textlen!=text.loc);

#ifndef __ti990__
	if ((ofile = open(ofname, O_WRONLY|O_CREAT|O_TRUNC, 0666)) < 0) {
#else
	if ((ofile = creat(ofname, 0700)) < 0) {
#endif
		printf("%s: can't create\n", ofname);
		exit(1);
	}
	outhdr();

	/* listing & output pass */
	if (1) {
		pass_gen = 1;
		if (lflag) pass_lst = 1;
		cfile   = -1;
		assemble();
	}
	oflush(&text);
	oflush(&data);

	/* relocate symbols, append to file & finish */
	symout();
	close(ofile);

	return 0;
}

/*
 * Open next input file
 */

int nextfile()
{
	if (++cfile >= nifiles) {
		return(0);
	}

	if (fd_in)
		close(fd_in);

	fd_in = open(ifiles[cfile], O_RDONLY);
	if (fd_in < 0) {
		printf("%s: can't open\n", ifiles[cfile]);
		exit(1);
	}
	line = 0;
	return(1);
}


/*
 * Print error message and continue
 */

static char *errtab [] = {
	"Previously defined absolute value required",
	"Short branch out of range",
	"Illegal or missing opcode",
	"Illegal data in .bss segement",
	"OEF or END within .if",
	"Garbage character",
	"Word value too large",
	"Improper nesting of .if and .endif",
	"Missing label",
	"Multiply defined symbol",
	"Number syntax",
	"Cannot move location counter backwards",
	"Symbol value changed between passes",
	"Missing quote",
	"Relocation error",
	"Missing symbol",
	"Undefined symbol",
	"Illegal value (e.g. register >15)",
	"Syntax error",
	"Division by zero",
	"Too many numeric labels",
	"Illegal map file",
};

int errcnt = 0;

void cerror(type)
{
	if (nifiles > 1)
		printf("%s: ", ifiles[cfile]);
	printf("%d: %s\n", line, errtab[type]);
	errcnt++;
}

/*
 * Print error message and abort current line
 */
void xerror(type)
{
	cerror(type);
	nexttoken = 0;
#ifndef __ti990__
	longjmp(err_jmp, 0);
#else
	reset();
#endif
}
