danwerner21/CortexPC/Software/historical informaton/v6unix-1.3.0/bbnnet/netuser.c

#define DEBUG
#include <sys/types.h>
#include <sys/ioctl.h>

#include "param.h"
#include "user.h"
#include "proc.h"
#include "sysnet.h"

#include "mbuf.h"
#include "net.h"
#include "ifcb.h"
#include "ip.h"
#include "tcp.h"
#include "raw.h"
#include "udp.h"
#include "ucb.h"
#include "fsm.h"

#define f_ucb f_offset

extern struct gway gates[NGATE], *gateway, *gateNGATE;
extern int ngate;

struct nfile {
	int n_flags;
	struct ucb *n_ucb;
};

static struct nfile nfiles[CMAPSIZ][10];
static struct netrequest requests[CMAPSIZ];

/*
 * Generate default local port number, if necessary and check if specified
 * connection is unique.
 */
u_short
uniqport(we, up, lport, fport)
struct netrequest *we;
register struct ucb *up;
register u_short lport, fport;
{
	register struct ucb *q;
	register i;
	int deflt = FALSE;

#ifdef DEBUGUNIQ
	printf ("uniqport: lport = %d, fport = %d, up = 0x%x\n",
		lport, fport, up);
#endif
	/* if local port is zero, make up a default */

	if (lport == 0) {
		for (q = netcb.n_ucb_hd, i = 0; q != NULL; q = q->uc_next, i++);
		lport = (i << 8) | ((int)up->uc_proc & 0xff);
#ifdef DEBUGUNIQ
		printf ("   lport-1 = %d, i = %d, pid = %d\n",
			lport, i, up->uc_proc);
#endif
		deflt++;
	}

	/* make sure port number is unique, for defaults, just increment
	   original choice until it is unique. */

tryagain:
	for (q = netcb.n_ucb_hd; q != NULL; q = q->uc_next) {
#ifdef DEBUGUNIQ
		printf ("   q = 0x%x\n", q);
#endif
		if (q != up && q->uc_host.s_addr == up->uc_host.s_addr &&
		    q->uc_local.s_addr == up->uc_local.s_addr &&
		    ((q->uc_flags & UTCP && q->uc_tcb != NULL &&
		      q->uc_tcb->t_lport == lport &&
		      q->uc_tcb->t_fport == fport) ||
		     (q->uc_flags & UUDP &&
		      q->uc_udp.u_lport == lport &&
		      q->uc_udp.u_fport == fport))) {
#ifdef DEBUGUNIQ
			printf ("   lport-2 = %d\n", lport);
#endif
			if (deflt)  {
				if (++lport < 0x100)
					lport = 0x100;
				goto tryagain;
			}
			break;
		}
	}

	/* if connection is unique, return local port, otherwise set error */

#ifdef DEBUGUNIQ
	printf ("   q = 0x%x, lport = %d\n", q, lport);
#endif
	if (q != NULL) {
		we->n_error = ENETRNG;
		return(0);
	}
	return(lport);
}

/*
 * TCP specific open routine.  Allocate a TCB and set up an open work request
 * for the finite state machine.
 */
int
tcpopen(we, up, cp)
struct netrequest *we;
register struct ucb *up;
register struct con *cp;
{
	register struct mbuf *m;
	register struct tcb *tp;
	register char *p;
	register i;

	/* allocate a buffer for a tcb */

	if ((m = m_get(1)) == NULL) {           /* no buffers */
		we->n_error = ENETBUF;
		return 0;
	}
	m->m_off = MHEAD;
	tp = mtod(m, struct tcb *);		/* -> tcb */
	we->n_tcb = tp;

	/* zero tcb for initialization */

	for (p = (char *)tp, i = MLEN; i > 0; i--)
		*p++ = 0;

	/* fill in ucb and tcb fields */

	tp->t_ucb = up;
	up->uc_tcb = tp;
	up->uc_flags |= UTCP;
	tp->t_fport = cp->c_fport;
	tp->t_lport = uniqport(we, up, cp->c_lport, cp->c_fport);

	/* if local port not unique, free tcb */

	if (we->n_error) {
		up->uc_flags &= ~UTCP;
		up->uc_tcb = NULL;
		m_free(m);
		return 0;
	}

	/*  make a user open work request for tcp */

	w_alloc((cp->c_mode & CONACT ? IUOPENR : IUOPENA), 0, tp, NULL, we);
	return 1;
}

/*
 * TCP read routine.  Copy data from the receive queue to user space.
 */
int
tcp_read(we, up, reent)
struct netrequest *we;
register struct ucb *up;
int reent;
{
	register struct tcb *tp;

	if ((tp = up->uc_tcb) == NULL) {
		we->n_error = ENETERR;
		return 0;
	}
	we->n_tcb = tp;

	if (!tp->syn_acked)		/* block if not connected */
		return 1;

	if (!reent) {
		we->n_datawait = FALSE;
		we->n_eol = FALSE;
		we->n_count = we->n_len;
	}

	if (we->n_datawait) {
	   if (up->uc_rbuf == NULL) {	/* no data available */
	      if (up->uc_state == 0) {
		 if (tp->fin_rcvd && rcv_empty(tp)) {
		    we->n_retval = we->n_count - we->n_len;
		    return 0;
		 }
	      }
	      return 1;
	   }
	   we->n_datawait = FALSE;
	}

#ifdef DEBUG
	printf ("tcp_read: n_slot = %d, n_len = %d(%d), buffer = 0x%x\n",
		we->n_slot, we->n_count, we->n_len, we->n_buffer);
#endif
	while (we->n_len > 0 && !we->n_eol) {

	        if (up->uc_rbuf != NULL) {	/* data available */
			register struct mbuf *m;
			int len;

			/* lock recieve buffer */

                        if (up->uc_flags & ULOCK) {
#ifdef DEBUG
				printf ("   ULOCKed\n");
#endif
                        	return 1;
			}
                        up->uc_flags |= ULOCK;

			/* copy the data an mbuf at a time */

			m = up->uc_rbuf;
                        while (m != NULL && we->n_len > 0 && !we->n_eol) {
#ifdef DEBUGDATA
				int ii, jj;
				unsigned char *jp;
#endif

                        	len = MIN(m->m_len, we->n_len);
#ifdef DEBUG
				printf ("   copyout: len = %d\n", len);
#ifdef DEBUGDATA
				jp = (unsigned char *)((int)m + m->m_off);
				for (ii = jj = 0; jj < len; ii++, jj++) {
				   printf (" 0x%x", *jp++ );
				   if (ii == 10) {printf("\n"); ii = 0;}
				}
				if (ii) printf ("\n");
#endif
#endif
                        	sysnet (SYSCOPYOUT, we->n_buffer, we->n_slot,
					(caddr_t)((int)m + m->m_off), len);
				we->n_buffer += len;
				we->n_len -= len;

				/* free or adjust mbuf */

                        	if (len == m->m_len) {
        			        we->n_eol = (int)m->m_act;
                        		m = m_free(m);
                        		--up->uc_rsize;
                        	} else {
                        		m->m_off += len;
                        		m->m_len -= len;
                        	}
                        }
			up->uc_rbuf = m;
			up->uc_flags &= ~ULOCK; /* unlock buffer */

			/*
			 * If any data was read, return even if the
			 * full read request was not satisfied
			 */
			if (we->n_count != we->n_len) {
				we->n_retval = we->n_count - we->n_len;
#ifdef DEBUG
				printf ("   len-1 = %d\n", we->n_retval);
#endif
				return 0;
			}
		} else if (up->uc_state == 0) {
			/*
			 * If no data left and foreign FIN rcvd, just
			 * return, otherwise make work request and wait
			 * for more data
			 */
			if (tp->fin_rcvd && rcv_empty(tp))
				break;

#ifdef DEBUG
			printf ("   w_alloc: len = %d\n", we->n_len);
#endif
        		w_alloc(IURECV, 0, tp, NULL, we);
			we->n_datawait = TRUE;
			return 1;
		} else {
			/*
			 * Net status to return.
			 */
			we->n_error = ENETSTAT;
			break;
		}
	}
	we->n_retval = we->n_count - we->n_len;
#ifdef DEBUG
	printf ("   len-2 = %d\n", we->n_retval);
#endif
	return 0;
}

/*
 * TCP write routine.  Copy data from user space to a net buffer chain.  Put
 * this chain on a send work request for the tcp fsm.
 */
int
tcp_write(we, up, reent)
struct netrequest *we;
register struct ucb *up;
int reent;
{
	register struct tcb *tp;

	if ((tp = up->uc_tcb) == NULL) {
		we->n_error = ENETERR;
		return 0;
	}
	we->n_tcb = tp;

	if (!tp->syn_acked)		/* block if not connected */
		return 1;

	if (!reent) {
		we->n_datawait = FALSE;
		we->n_count = we->n_len;
	}
#ifdef DEBUG
	printf ("tcp_write: n_slot = %d, n_len = %d(%d)\n",
		we->n_slot, we->n_count, we->n_len);
#endif

	while (we->n_len > 0 && up->uc_state == 0) {
		register struct mbuf *n;
		register int bufs;
		struct {
			struct mbuf *top;
		} nn;

		/* #bufs can send now */

		bufs = (int)up->uc_snd - (int)up->uc_ssize;
#ifdef DEBUG
		printf ("   bufs = %d\n", bufs);
#endif

		/* top of chain to send */

		nn.top = NULL;
		n = (struct mbuf *)&nn;

		/* copy data from user to mbuf chain for send work req */

        	while (bufs-- > 0 && we->n_len > 0) {
			register struct mbuf *m;
			register int len;
#ifdef DEBUGDATA
			int ii, jj;
			unsigned char *jp;
#endif

			/* set up an mbuf */

			we->n_datawait = FALSE;
        		if ((m = m_get(1)) == NULL) {
				/* send what we have, make work req */
				if (nn.top)
        				w_alloc(IUSEND, 0, tp, nn.top, we);
#ifdef DEBUG
				printf ("   w_alloc-1: len = %d\n", we->n_len);
#endif
				return 1;
			}
        		m->m_off = MHEAD;

			/* copy user data in */

        		len = MIN(MLEN, we->n_len);
        		sysnet (SYSCOPYIN, (caddr_t)((int)m + m->m_off),
				we->n_buffer, we->n_slot, len);
#ifdef DEBUG
				printf ("   copyin: len = %d\n", len);
#ifdef DEBUGDATA
				jp = (unsigned char *)((int)m + m->m_off);
				for (ii = jj = 0; jj < len; ii++, jj++) {
				   printf (" 0x%x", *jp++ );
				   if (ii == 10) {printf("\n"); ii = 0;}
				}
				if (ii) printf ("\n");
#endif
#endif
        		we->n_buffer += len;
			we->n_len -= len;

			/* chain to work request mbufs */

        		m->m_len = len;
        		n->m_next = m;
        		n = m;
        	}

		if (!we->n_datawait) {
		   w_alloc(IUSEND, 0, tp, nn.top, we);         /* make work req */
#ifdef DEBUG
		   printf ("   w_alloc-2: len = %d, bufs = %d\n",
				we->n_len, bufs + 1);
#endif
		}

		/* if more to send, sleep on more buffers */

		if (we->n_len > 0) {
		        we->n_datawait = TRUE;
			return 1;
		}
	}
	we->n_retval = we->n_count;
	return 0;
}

int
tcp_close (we, up, reent)
struct netrequest *we;
register struct ucb *up;
int reent;
{
	register struct tcb *tp;

	if (up->uc_flags & UTCP) {      /* tcp connection */

		tp = up->uc_tcb;

		/* if connection has not already been closed, by user or
		   system, enqueue work request.  otherwise, if the tcb
		   has been deleted (completed close), then release the ucb */

		if (tp != NULL) {	/* tcb still exists */
			tp->usr_abort = TRUE;	/* says we've closed */
			if (!tp->usr_closed) {
				w_alloc(IUCLOSE, 0, tp, up, we);
				return 1;
			}
		}

	} else if (up->uc_flags&(UIP+URAW+UUDP)) {        /* raw connection */

	/* free ucb and lower system buffer allocation */

        	netcb.n_lowat -= up->uc_snd + up->uc_rcv + 2;
		netcb.n_hiwat = (netcb.n_lowat * 3) >> 1;
		if (up->uc_route != NULL) {
        		h_free(up->uc_route);
			up->uc_route = NULL;
		}
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
